modern-hobbyist/aesir/stm32G474RETx-template/stm32G474RETx-template.kicad_pcb

## KiCad design stm32G474RETx-template/stm32G474RETx-template.kicad_pcb (2025-07-10)

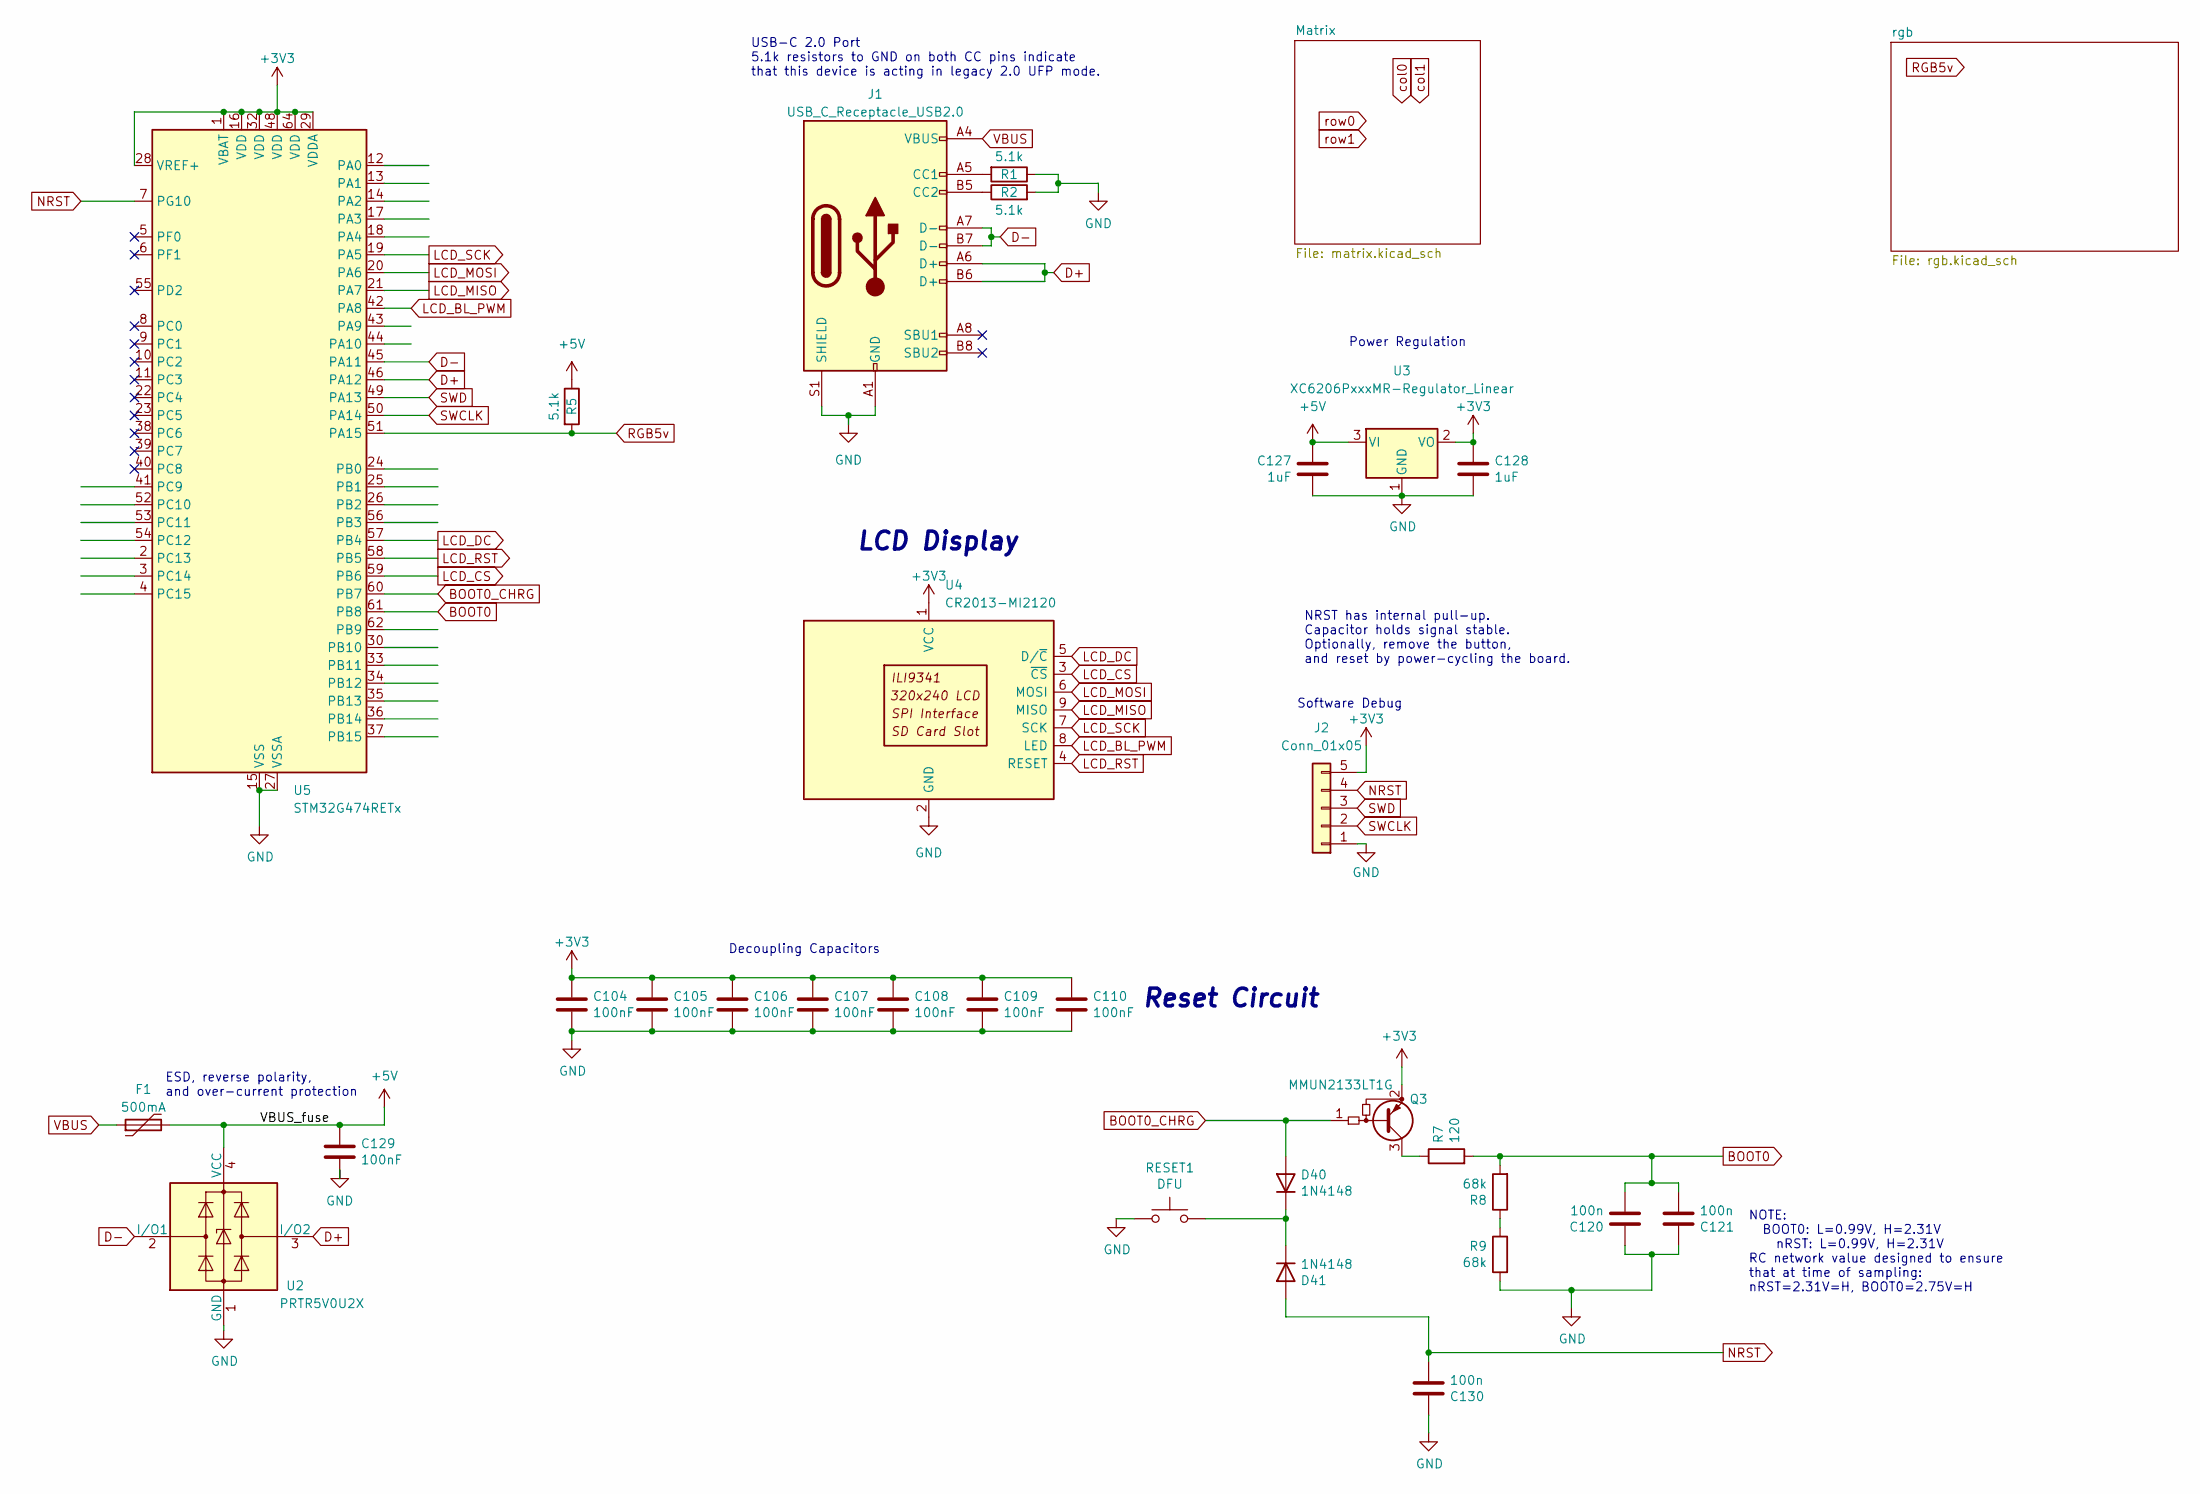
[picture p12: schematic stm32G474RETx-template.kicad_sch]

Parts:
C104, C105, C106, C107, C108, C109, C110, C129: 100nF; C_0402_1005Metric; LCSC C307331
C120, C121, C130: 100n; C_0805_2012Metric
C127, C128: 1uF; C_0402_1005Metric; LCSC C307331
D40, D41: 1N4148; D_SOD-123
F1: 500mA; Fuse_1206_3216Metric; LCSC C135341
J1: USB_C_Receptacle_USB2.0; USB_C_Receptacle_HRO_TYPE-C-31-M-12; JlcRotOffset 180
J2: Conn_01x05; PinHeader_1x05_P2.54mm_Vertical
Q3: MMUN2133LT1G; SOT-23-3
R1, R2, R5: 5.1k; R_0402_1005Metric
R7: 120; R_0805_2012Metric
R8, R9: 68k; R_0805_2012Metric
RESET1: DFU; SW_SPST_TL3342
U2: PRTR5V0U2X; SOT-143; LCSC C2827688
U3: XC6206PxxxMR-Regulator_Linear; SOT-23; LCSC C5446
U4: CR2013-MI2120
U5: STM32G474RETx; LQFP-64_10x10mm_P0.5mm

Connections:
+3V3: C104.1, C105.1, C106.1, C107.1, C108.1, C109.1, C110.1, C128.1, J2.5, Q3.2 (E), U3.2 (VO), U4.1 (VCC), U5.1 (VBAT), U5.16 (VDD), U5.28 (VREF+), U5.29 (VDDA), U5.32 (VDD), U5.48 (VDD), U5.64 (VDD)
+5V: C127.1, C129.1, F1.2, R5.1, U2.4 (VCC), U3.3 (VI); also elsewhere on the board
BOOT0: C120.2, C121.2, R7.2, R8.2, U5.61 (PB8)
BOOT0_CHRG: D40.2 (A), Q3.1 (B), U5.60 (PB7)
D+: J1.A6 (D+), J1.B6 (D+), U2.3 (I/O2), U5.46 (PA12)
D-: J1.A7 (D-), J1.B7 (D-), U2.2 (I/O1), U5.45 (PA11)
GND: C104.2, C105.2, C106.2, C107.2, C108.2, C109.2, C110.2, C120.1, C121.1, C127.2, C128.2, C129.2, C130.1, J1.A1 (GND), J1.A12 (GND), J1.B1 (GND), J1.B12 (GND), J1.S1 (SHIELD), J2.1, R1.1, R2.2, R9.2, RESET1.1, U2.1 (GND), U3.1 (GND), U4.2 (GND), U5.15 (VSS), U5.27 (VSSA), U5.31 (VSS), U5.47 (VSS), U5.63 (VSS); also elsewhere on the board
LCD_BL_PWM: U4.8 (LED), U5.42 (PA8)
LCD_CS: U4.3 (~CS), U5.59 (PB6)
LCD_DC: U4.5 (D/~C), U5.57 (PB4)
LCD_MISO: U4.9 (MISO), U5.21 (PA7)
LCD_MOSI: U4.6 (MOSI), U5.20 (PA6)
LCD_RST: U4.4 (RESET), U5.58 (PB5)
LCD_SCK: U4.7 (SCK), U5.19 (PA5)
NRST: C130.2, D41.2 (A), J2.4, U5.7 (PG10)
unnamed: D40.1 (K), D41.1 (K), RESET1.2
unnamed: J1.A5 (CC1), R1.2
unnamed: J1.B5 (CC2), R2.1
unnamed: Q3.3 (C), R7.1
unnamed: R8.1, R9.1
RGB5v: R5.2, U5.51 (PA15); also elsewhere on the board
SWCLK: J2.2, U5.50 (PA14)
SWD: J2.3, U5.49 (PA13)
VBUS: F1.1, J1.A4 (VBUS), J1.A9 (VBUS), J1.B4 (VBUS), J1.B9 (VBUS)

Notes on the sheet:
Decoupling Capacitors
NOTE: BOOT0: L=0.99V, H=2.31V nRST: L=0.99V, H=2.31V RC network value designed to ensure that at time of sampling: nRST=2.31V=H, BOOT0=2.75V=H
Power Regulation
Reset Circuit
USB-C 2.0 Port 5.1k resistors to GND on both CC pins indicate that this device is acting in legacy 2.0 UFP mode.
ESD, reverse polarity, and over-current protection
Software Debug
NRST has internal pull-up. Capacitor holds signal stable. Optionally, remove the button, and reset by power-cycling the board.
LCD Display

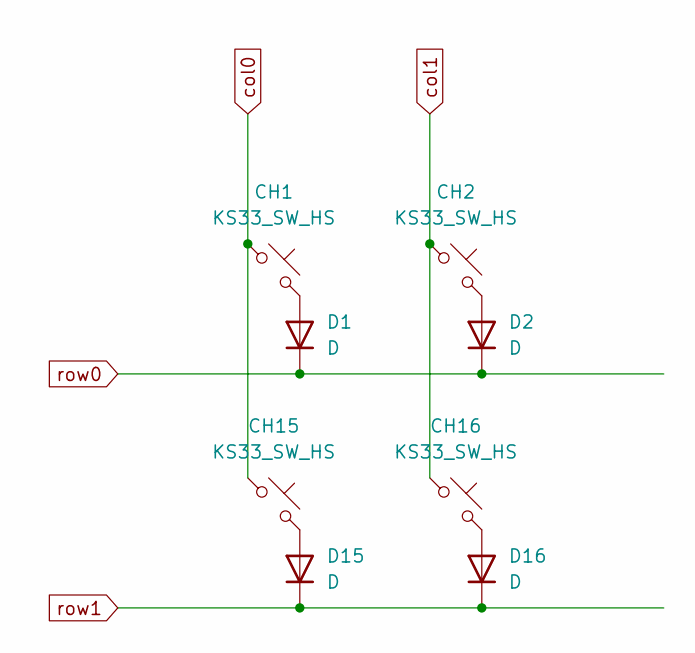
[picture p13: schematic matrix.kicad_sch]

Parts:
CH1, CH2, CH15, CH16: KS33_SW_HS; KS-33_MX-Hotswap-1U
D1, D2, D15, D16: D; D_SOD-123

Connections:
unnamed: CH1.2, D1.2 (A)
unnamed: CH2.2, D2.2 (A)
unnamed: CH15.2, D15.2 (A)
unnamed: CH16.2, D16.2 (A)
col0: CH1.1, CH15.1
col1: CH2.1, CH16.1
row0: D1.1 (K), D2.1 (K)
row1: D15.1 (K), D16.1 (K)

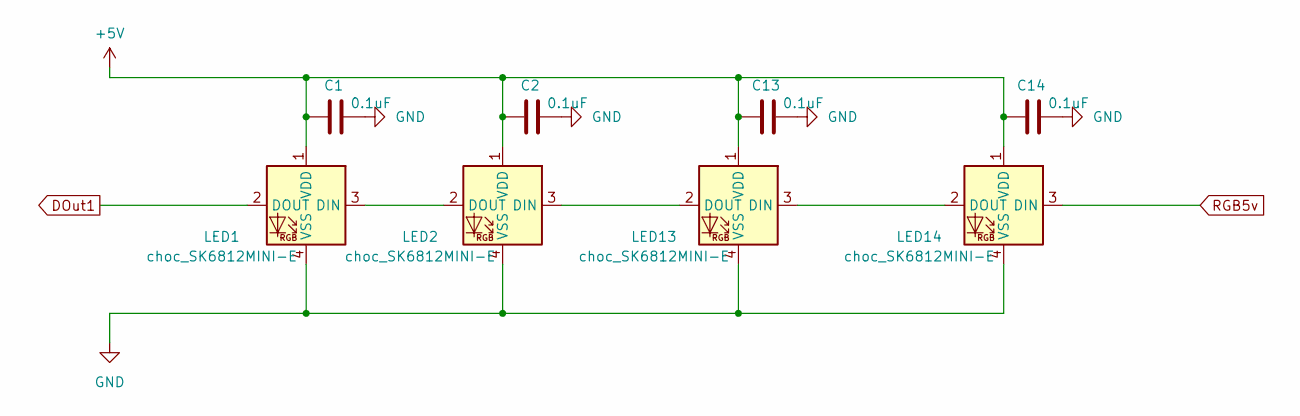
[picture p14: schematic rgb.kicad_sch]

Parts:
C1, C2, C13, C14: 0.1uF; C_0402_1005Metric
LED1, LED2, LED13, LED14: choc_SK6812MINI-E; LED_choc_6028R

Connections:
+5V: C1.1, C2.1, C13.1, C14.1, LED1.1 (VDD), LED2.1 (VDD), LED13.1 (VDD), LED14.1 (VDD); also elsewhere on the board
DOut1: LED1.2 (DOUT)
GND: C1.2, C2.2, C13.2, C14.2, LED1.4 (VSS), LED2.4 (VSS), LED13.4 (VSS), LED14.4 (VSS); also elsewhere on the board
unnamed: LED1.3 (DIN), LED2.2 (DOUT)
unnamed: LED13.3 (DIN), LED14.2 (DOUT)
unnamed: LED2.3 (DIN), LED13.2 (DOUT)
RGB5v: LED14.3 (DIN); also elsewhere on the board

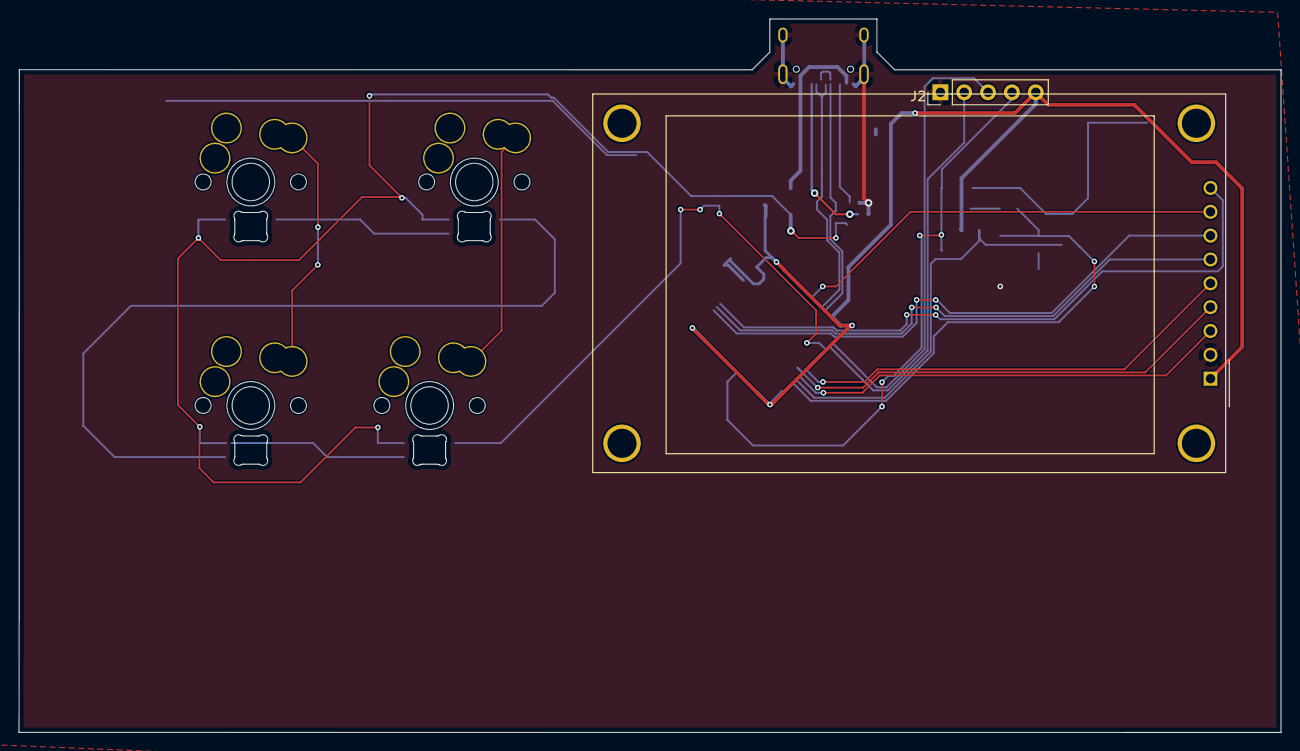
[picture p15: board stm32G474RETx-template.kicad_pcb from above]

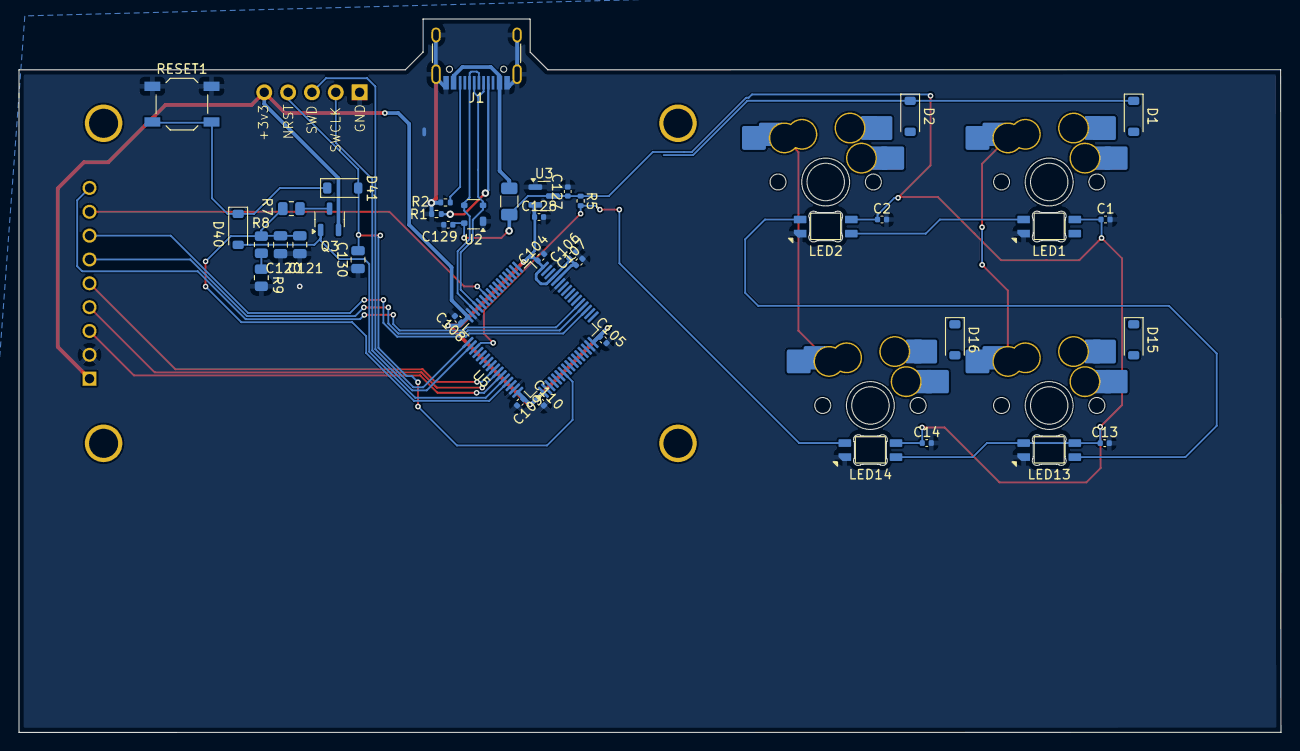
[picture p16: board stm32G474RETx-template.kicad_pcb from below]

Board: 2 copper layers, 134.5 x 76.0 mm, 46 parts (44 on the bottom side), 35 nets.
