modern-hobbyist/aesir/modern-keyboard-template/modern-keyboard-template.kicad_pcb

## KiCad design modern-keyboard-template/modern-keyboard-template.kicad_pcb (2024-09-18)

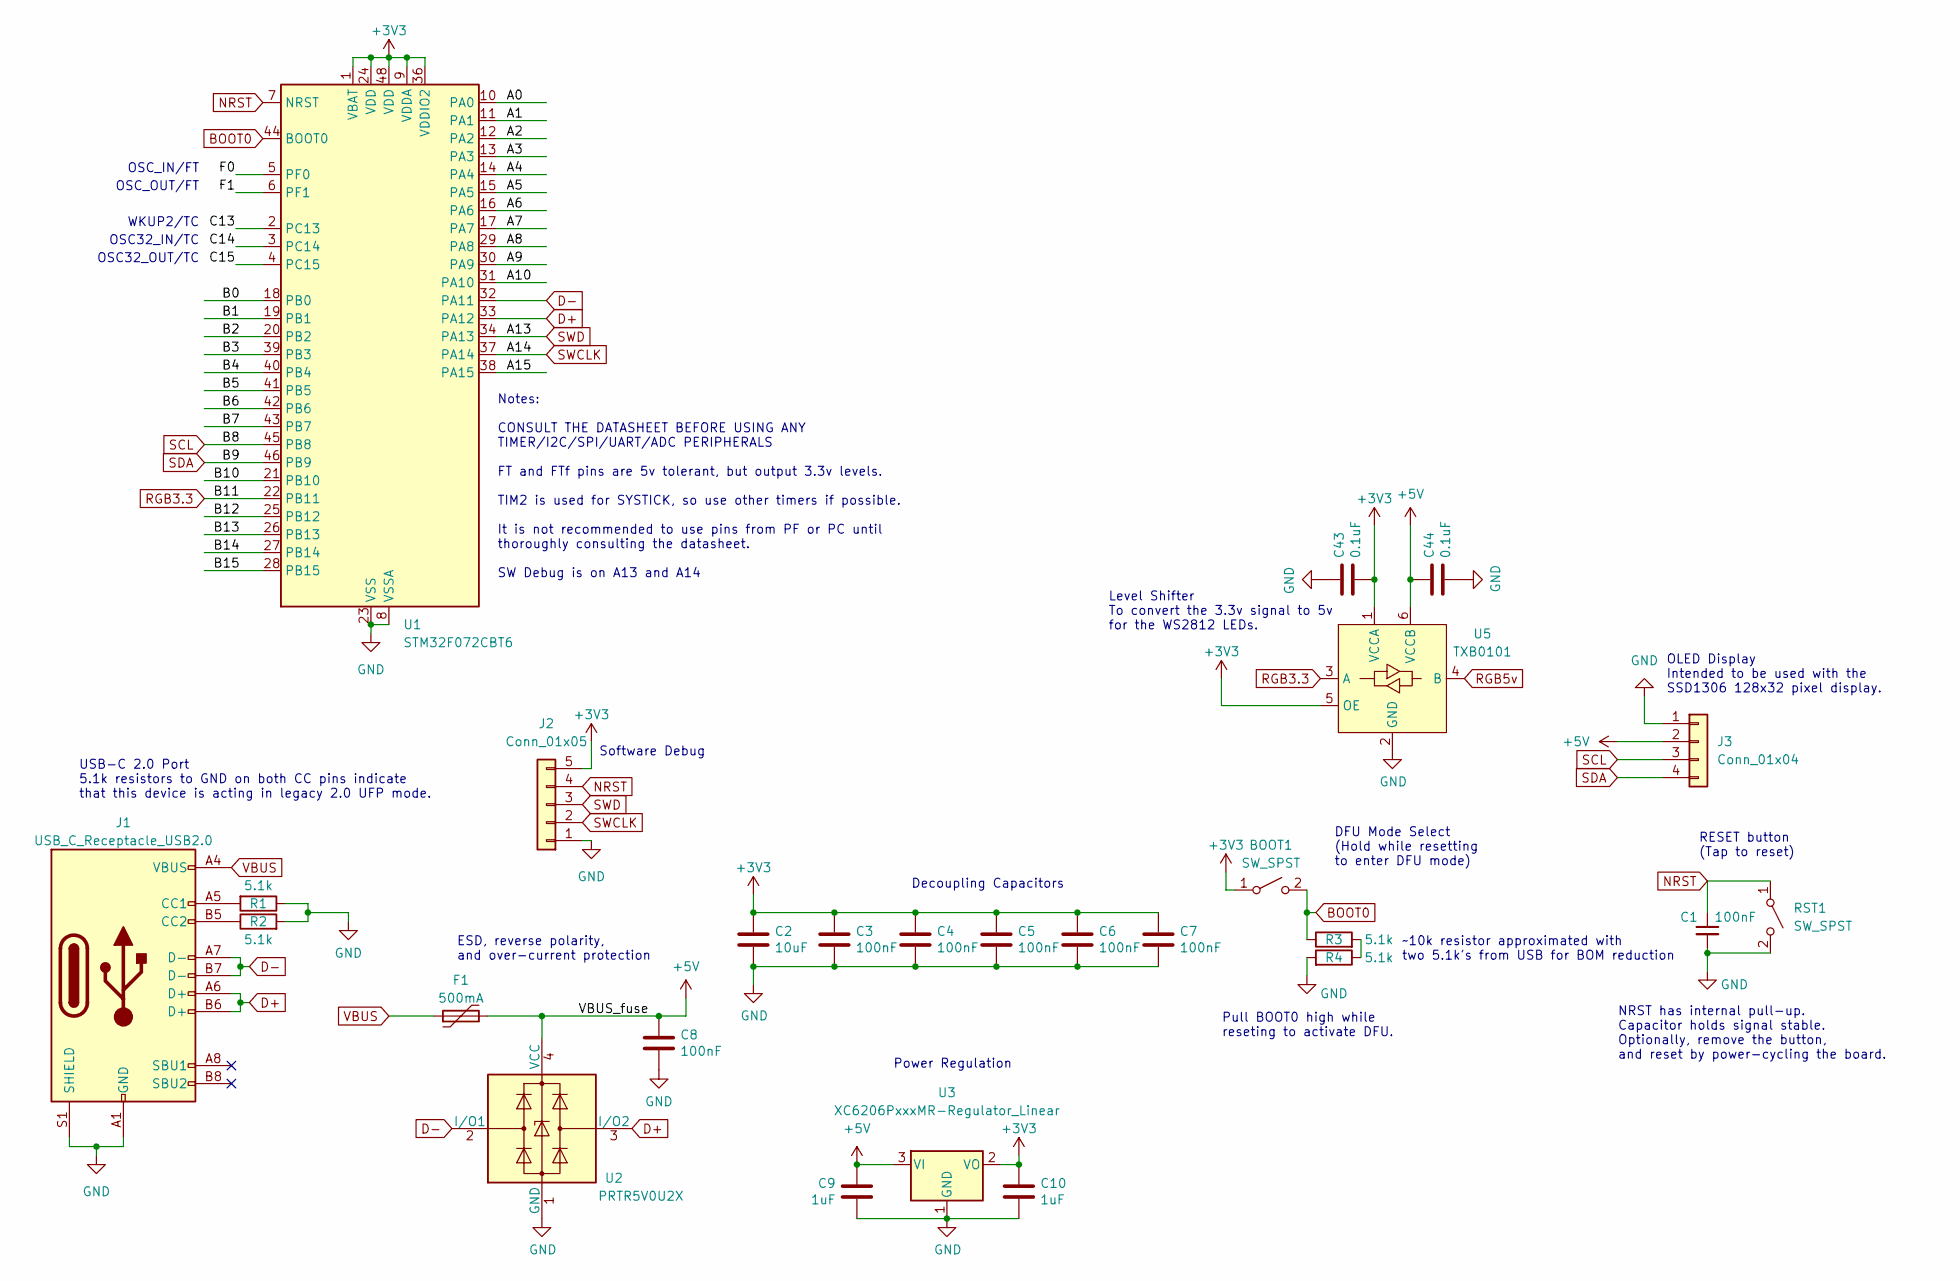
[picture p17: schematic modern-keyboard-template.kicad_sch]

Parts:
BOOT1: SW_SPST; SW_SPST_TL3342
C1, C3, C4, C5, C6, C7, C8: 100nF; C_0402_1005Metric; LCSC C307331
C2: 10uF; C_0603_1608Metric; LCSC C307331
C9, C10: 1uF; C_0402_1005Metric; LCSC C307331
C43, C44: 0.1uF; C_0402_1005Metric; LCSC C307331
F1: 500mA; Fuse_1206_3216Metric; LCSC C135341
J1: USB_C_Receptacle_USB2.0; USB_C_Receptacle_HRO_TYPE-C-31-M-12; JlcRotOffset 180
J2: Conn_01x05; PinHeader_1x05_P2.54mm_Vertical
J3: Conn_01x04; SSD1306-0.91-OLED-4pin-128x32
R1, R2, R3, R4: 5.1k; R_0402_1005Metric
RST1: SW_SPST; SW_SPST_TL3342
U1: STM32F072CBT6; LQFP-48_7x7mm_P0.5mm; JlcRotOffset 90
U2: PRTR5V0U2X; SOT-143; LCSC C2827688
U3: XC6206PxxxMR-Regulator_Linear; SOT-23; LCSC C5446
U5: TXB0101; SOT-363_SC-70-6_Handsoldering; LCSC C324081

Connections:
+3V3: BOOT1.1 (A), C2.1, C3.1, C4.1, C5.1, C6.1, C7.1, C10.1, C43.2, J2.5, U1.1 (VBAT), U1.9 (VDDA), U1.24 (VDD), U1.36 (VDDIO2), U1.48 (VDD), U3.2 (VO), U5.1 (VCCA), U5.5 (OE)
+5V: C8.1, C9.1, C44.1, F1.2, J3.2, U2.4 (VCC), U3.3 (VI), U5.6 (VCCB)
/A0: U1.10 (PA0)
/A1: U1.11 (PA1)
/A2: U1.12 (PA2)
/A3: U1.13 (PA3)
/A4: U1.14 (PA4)
/A5: U1.15 (PA5)
/A6: U1.16 (PA6)
/A7: U1.17 (PA7)
/A8: U1.29 (PA8)
/A9: U1.30 (PA9)
/A10: U1.31 (PA10)
/A15: U1.38 (PA15)
/B0: U1.18 (PB0)
/B1: U1.19 (PB1)
/B2: U1.20 (PB2)
/B3: U1.39 (PB3)
/B4: U1.40 (PB4)
/B5: U1.41 (PB5)
/B6: U1.42 (PB6)
/B7: U1.43 (PB7)
/B10: U1.21 (PB10)
/B12: U1.25 (PB12)
/B13: U1.26 (PB13)
/B14: U1.27 (PB14)
/B15: U1.28 (PB15)
/C13: U1.2 (PC13)
/C14: U1.3 (PC14)
/C15: U1.4 (PC15)
/F0: U1.5 (PF0)
/F1: U1.6 (PF1)
BOOT0: BOOT1.2 (B), R3.1, U1.44 (BOOT0)
D+: J1.A6 (D+), J1.B6 (D+), U1.33 (PA12), U2.3 (I/O2)
D-: J1.A7 (D-), J1.B7 (D-), U1.32 (PA11), U2.2 (I/O1)
GND: C1.2, C2.2, C3.2, C4.2, C5.2, C6.2, C7.2, C8.2, C9.2, C10.2, C43.1, C44.2, J1.A1 (GND), J1.A12 (GND), J1.B1 (GND), J1.B12 (GND), J1.S1 (SHIELD), J2.1, J3.1, R1.1, R2.2, R4.2, RST1.2 (B), U1.8 (VSSA), U1.23 (VSS), U1.35 (VSS), U1.47 (VSS), U2.1 (GND), U3.1 (GND), U5.2 (GND)
NRST: C1.1, J2.4, RST1.1 (A), U1.7 (NRST)
unnamed: J1.A5 (CC1), R1.2
unnamed: J1.B5 (CC2), R2.1
unnamed: R3.2, R4.1
RGB3.3: U1.22 (PB11), U5.3 (A)
RGB5v: U5.4 (B)
SCL: J3.3, U1.45 (PB8)
SDA: J3.4, U1.46 (PB9)
SWCLK: J2.2, U1.37 (PA14)
SWD: J2.3, U1.34 (PA13)
VBUS: F1.1, J1.A4 (VBUS), J1.A9 (VBUS), J1.B4 (VBUS), J1.B9 (VBUS)

Notes on the sheet:
Decoupling Capacitors
~10k resistor approximated with two 5.1k's from USB for BOM reduction
Notes: CONSULT THE DATASHEET BEFORE USING ANY TIMER/I2C/SPI/UART/ADC PERIPHERALS FT and FTf pins are 5v tolerant, but output 3.3v levels. TIM2 is used for SYSTICK, so use other timers if possible. It is not recommended to use pins from PF or PC until thoroughly consulting the datasheet. SW Debug is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
RESET button (Tap to reset)
Power Regulation
OSC_IN/FT
OLED Display Intended to be used with the SSD1306 128x32 pixel display.
OSC32_OUT/TC
USB-C 2.0 Port 5.1k resistors to GND on both CC pins indicate that this device is acting in legacy 2.0 UFP mode.
WKUP2/TC
OSC_OUT/FT
ESD, reverse polarity, and over-current protection
Software Debug
NRST has internal pull-up. Capacitor holds signal stable. Optionally, remove the button, and reset by power-cycling the board.
OSC32_IN/TC
Pull BOOT0 high while reseting to activate DFU.
Level Shifter To convert the 3.3v signal to 5v for the WS2812 LEDs.
DFU Mode Select (Hold while resetting to enter DFU mode)

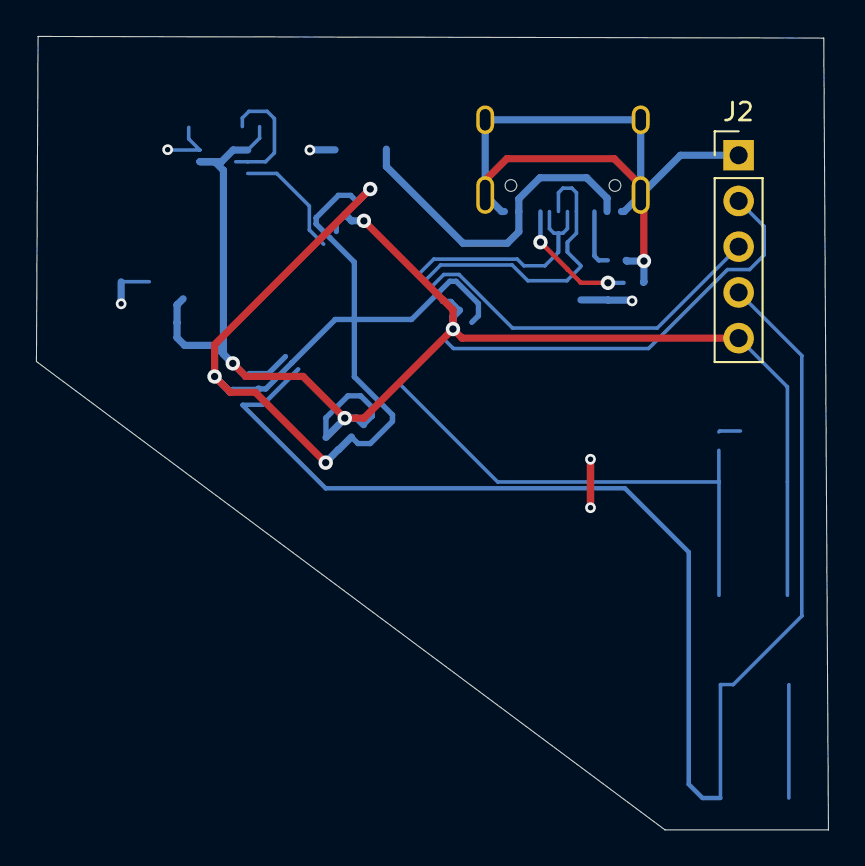
[picture p18: board modern-keyboard-template.kicad_pcb from above]

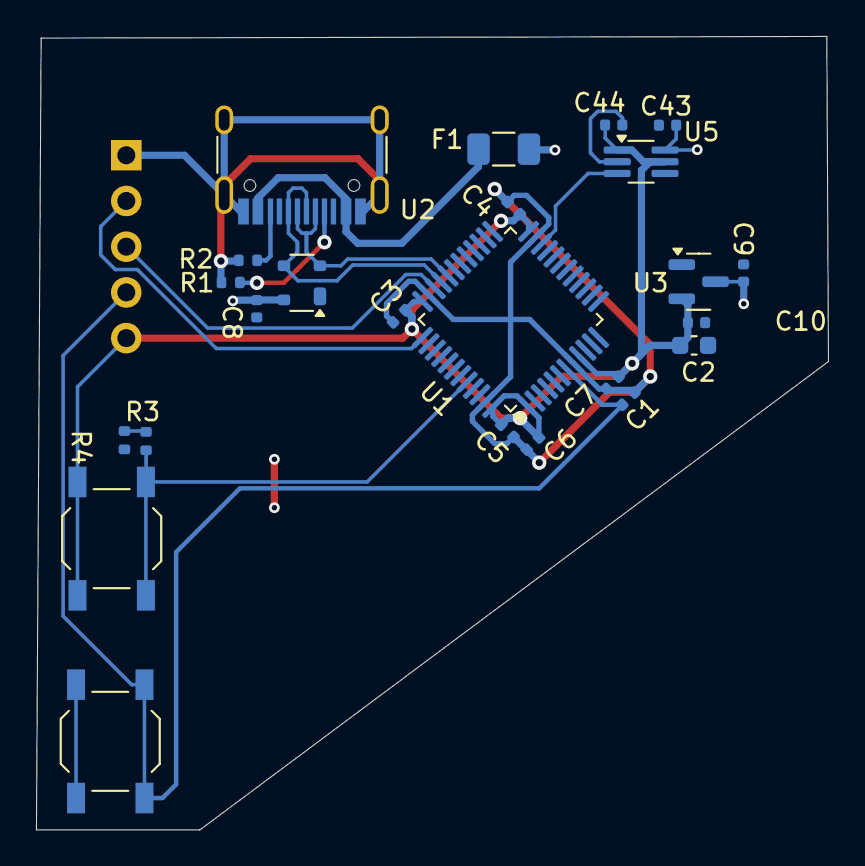
[picture p19: board modern-keyboard-template.kicad_pcb from below]

Board: 2 copper layers, 44.0 x 44.1 mm, 25 parts (24 on the bottom side), 14 nets.
